11lein/Soundboard/docu/20230720_220250.jpg

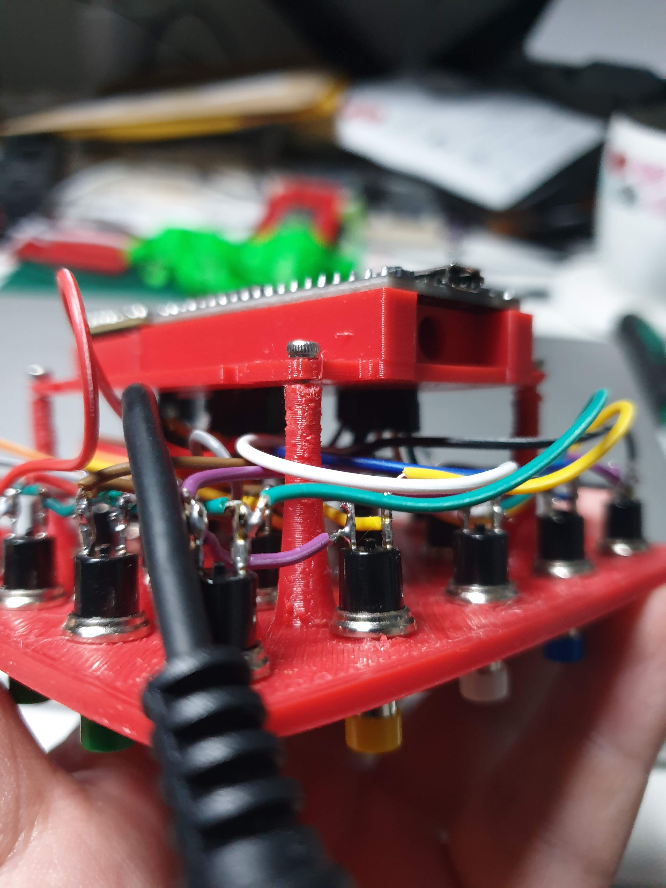
docu/20230720_220250.jpg
