11lein/Soundboard/docu/20230727_214752 (1).jpg

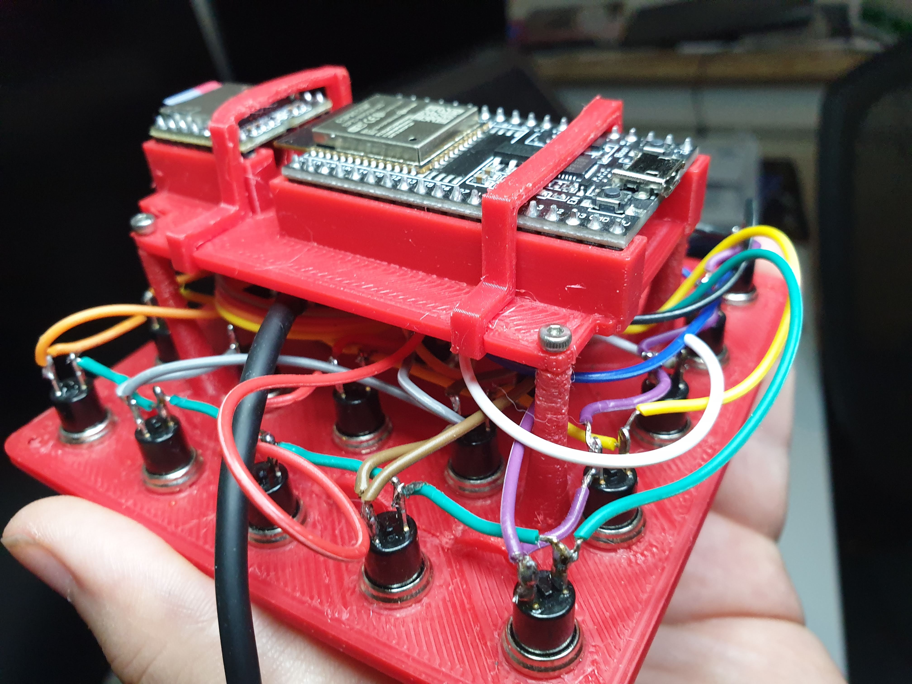
docu/20230727_214752 (1).jpg
